Wierzbowsky/4116TesterMod/Pics/case1.jpg

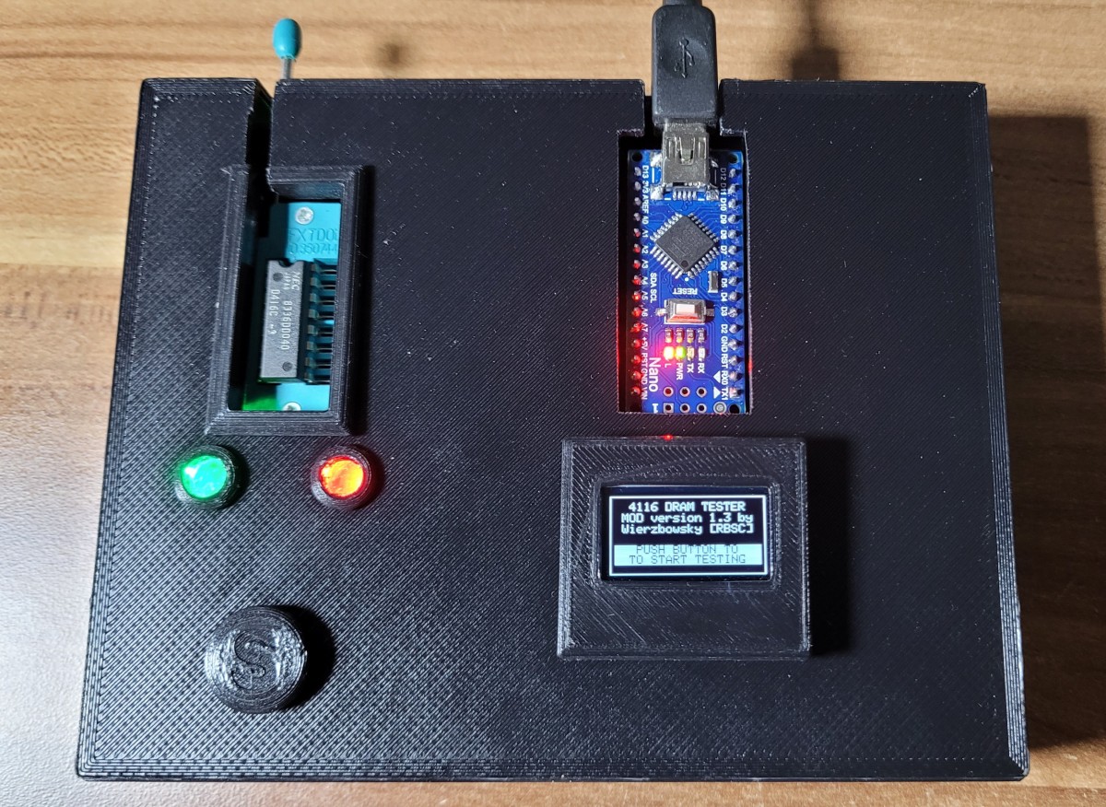
Pics/case1.jpg
