Wierzbowsky/4116TesterMod/Pics/case_open.jpg

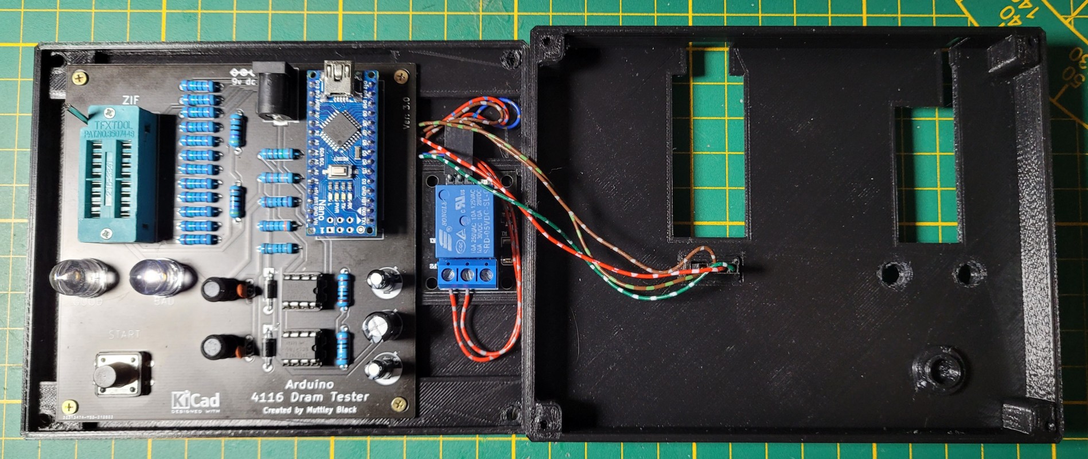
Pics/case_open.jpg
