Wierzbowsky/4116TesterMod/Pics/bom_partslist.png

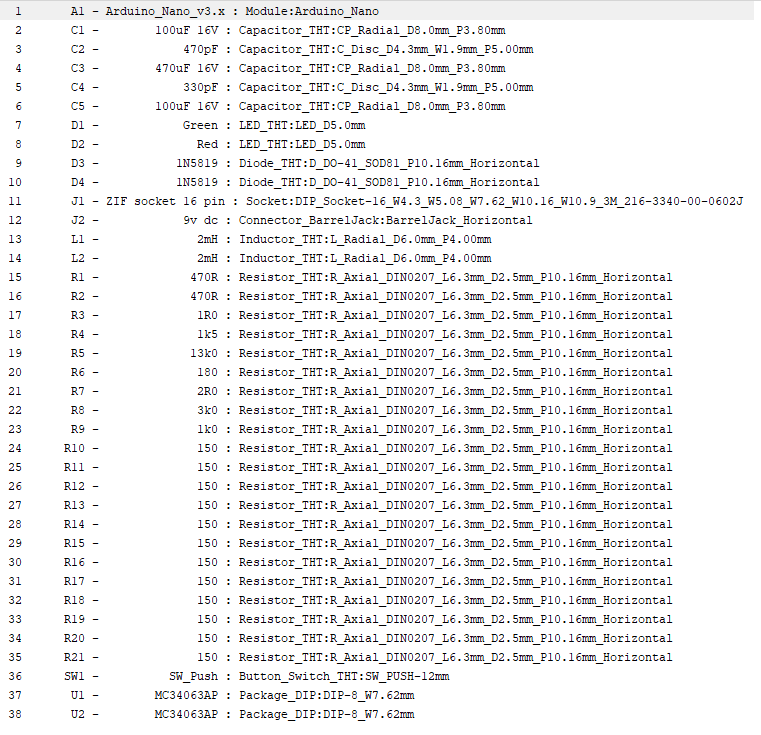
Pics/bom_partslist.png
